honeydewsleep/wildchild/preview/matched_base_cut.png

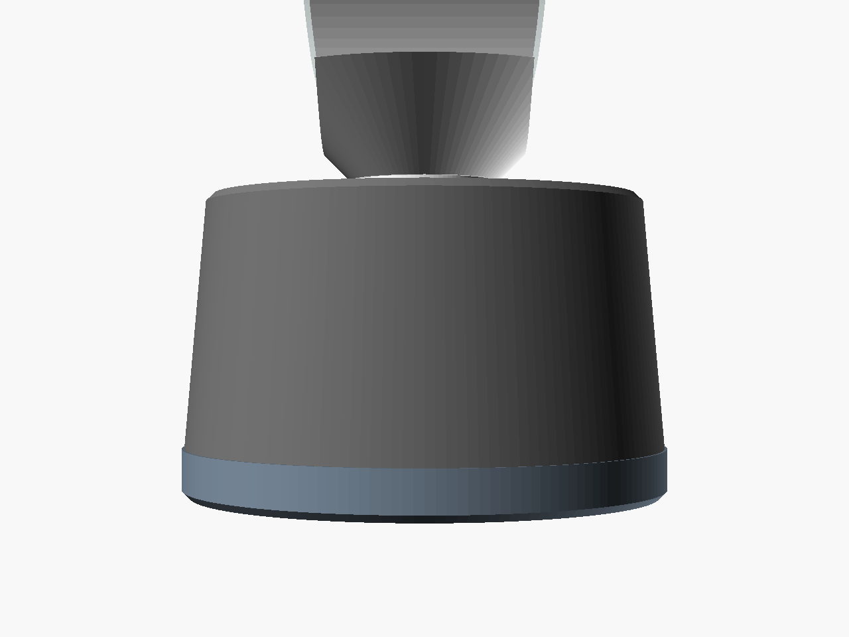
preview/matched_base_cut.png
