honeydewsleep/wildchild/preview/shape_options.png

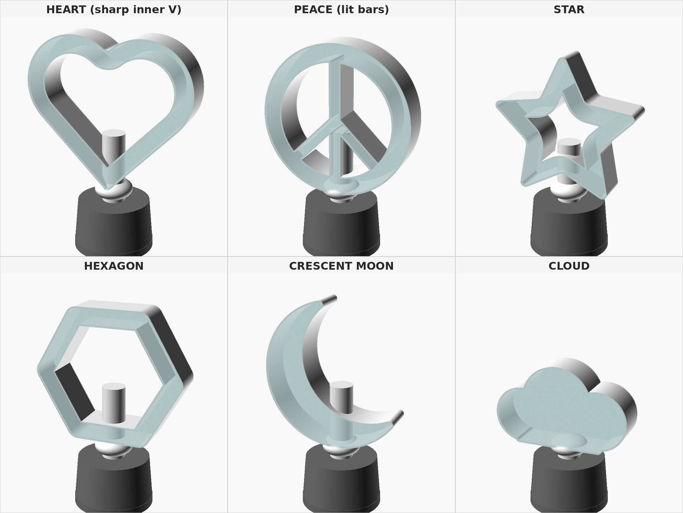
preview/shape_options.png
