honeydewsleep/wildchild/stl/capsule_funnel_00.stl

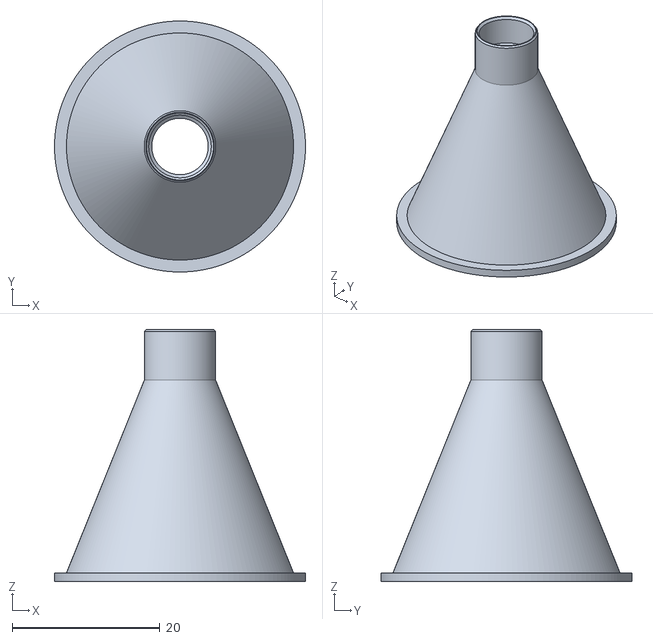
[picture p23: CAD file, 2026-10-06]
stl/capsule_funnel_00.stl
34.0 x 34.0 x 34.2
