honeydewsleep/wildchild/stl/shell_free_port_button.stl

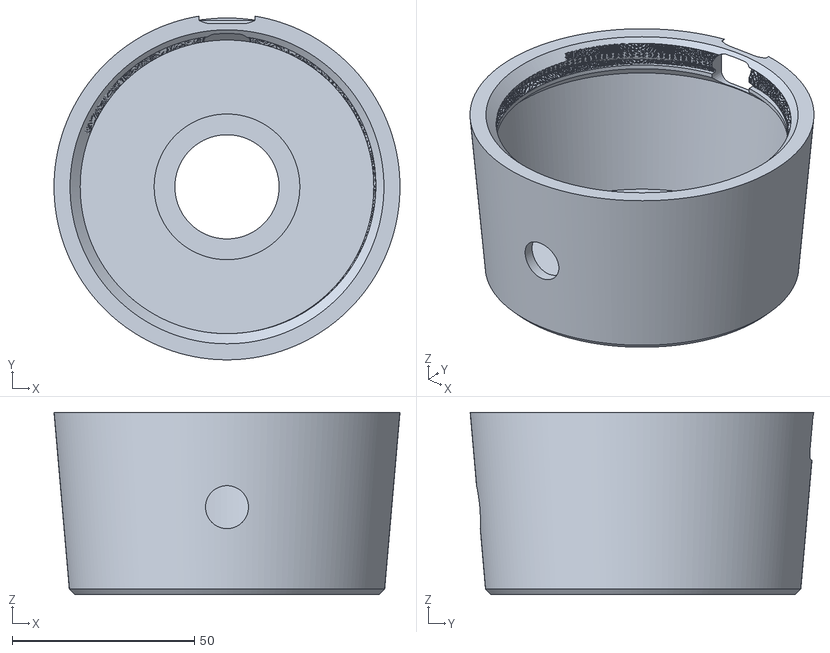
[picture p24: CAD file, 2026-08-14]
stl/shell_free_port_button.stl
95.0 x 94.4 x 50.0
