honeydewsleep/wildchild/stl/chassis_jack.stl

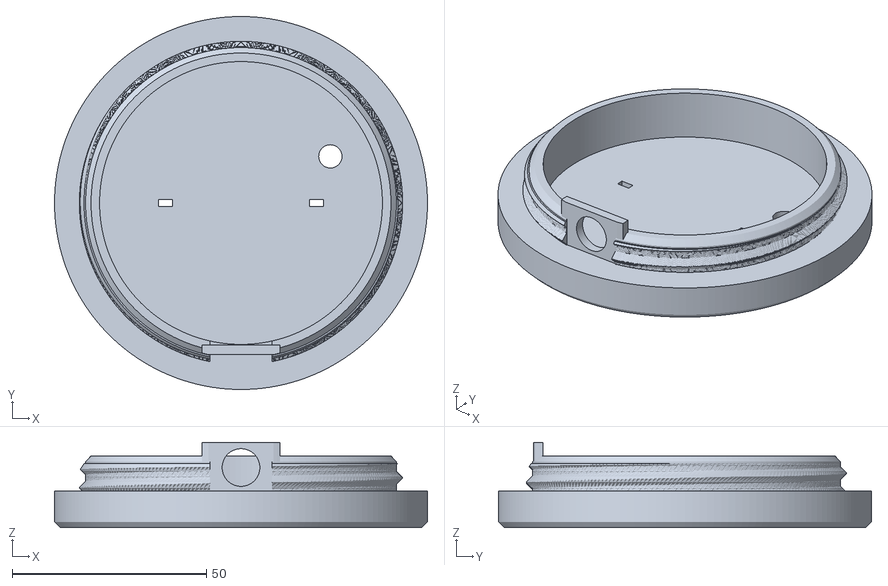
[picture p25: CAD file, 2026-08-14]
stl/chassis_jack.stl
96.0 x 96.0 x 22.0
