honeydewsleep/wildchild/stl/shell_free_jack_button.stl

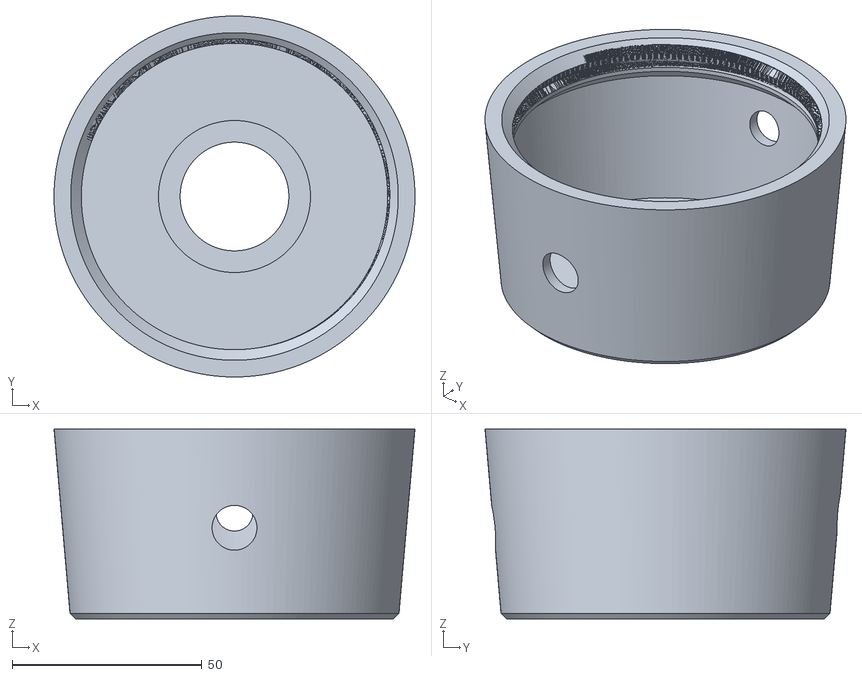
[picture p26: CAD file, 2026-08-13]
stl/shell_free_jack_button.stl
95.0 x 95.0 x 50.0
