honeydewsleep/wildchild/stl/shell_free_button7.stl

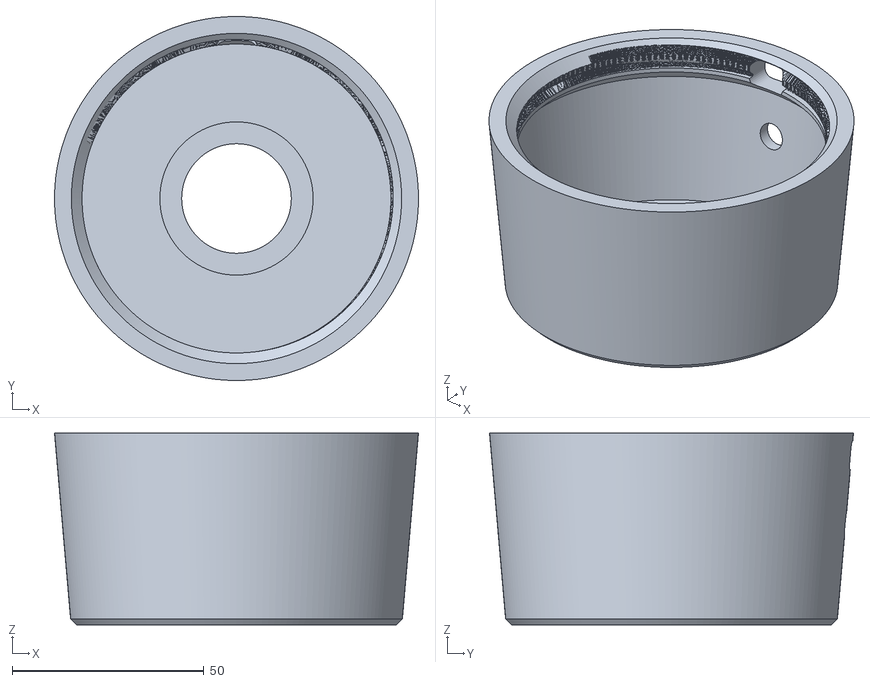
[picture p27: CAD file, 2026-08-11]
stl/shell_free_button7.stl
95.0 x 95.0 x 50.0
