honeydewsleep/wildchild/stl/ring_double_sided.stl

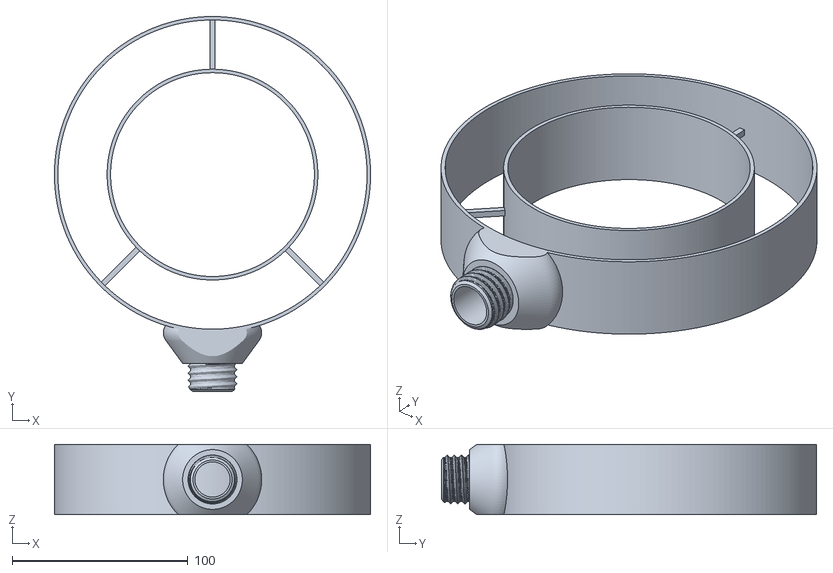
[picture p28: CAD file, 2026-07-26]
stl/ring_double_sided.stl
180.0 x 213.5 x 40.0
