honeydewsleep/wildchild/stl/ring_ds_diffuser.stl

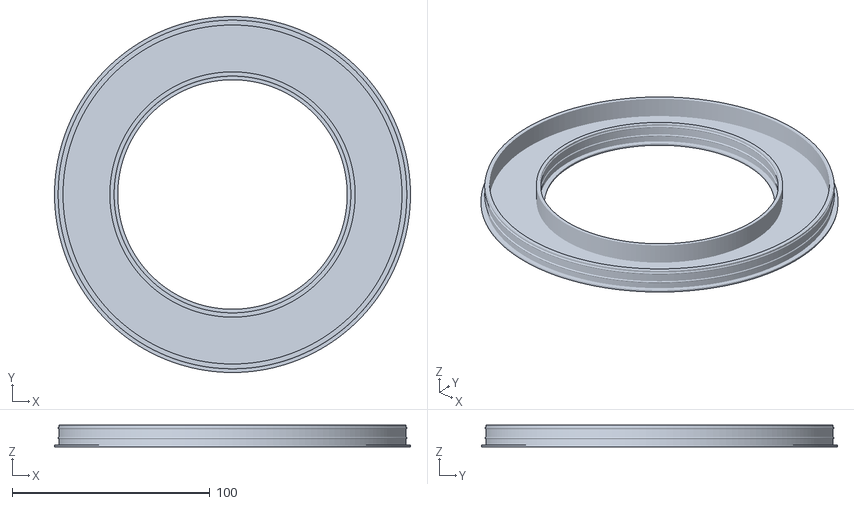
[picture p29: CAD file, 2026-07-26]
stl/ring_ds_diffuser.stl
180.0 x 180.0 x 11.0
