honeydewsleep/wildchild/stl/ring_diffuser.stl

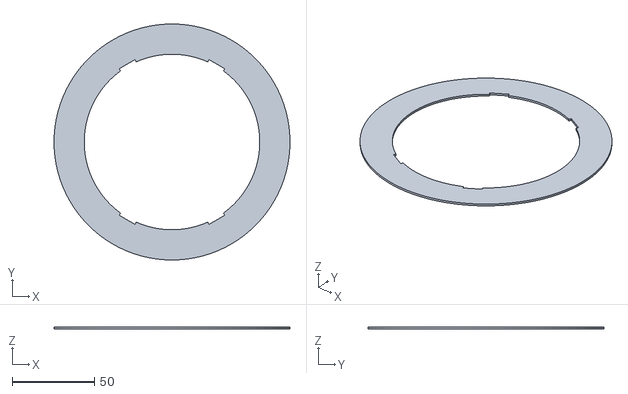
[picture p30: CAD file, 2026-07-26]
stl/ring_diffuser.stl
143.4 x 143.4 x 1.20
