honeydewsleep/wildchild/stl/stem_locknut.stl

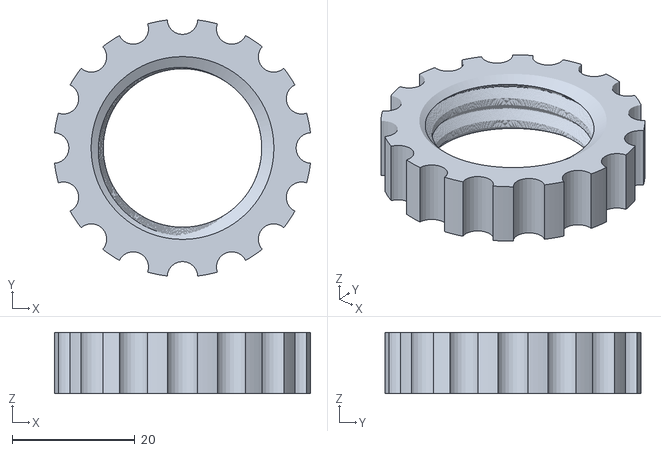
[picture p31: CAD file, 2026-07-26]
stl/stem_locknut.stl
41.7 x 41.7 x 10.0
