honeydewsleep/wildchild/stl/shell_threaded.stl

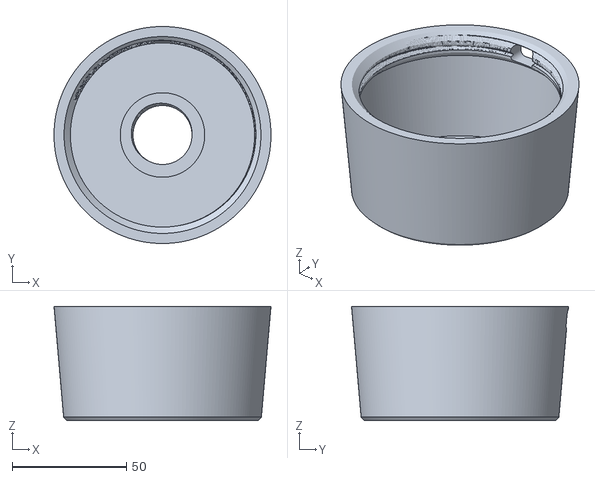
[picture p32: CAD file, 2026-07-26]
stl/shell_threaded.stl
95.0 x 95.0 x 50.0
