honeydewsleep/wildchild/stl/chassis_bat_flat8.stl

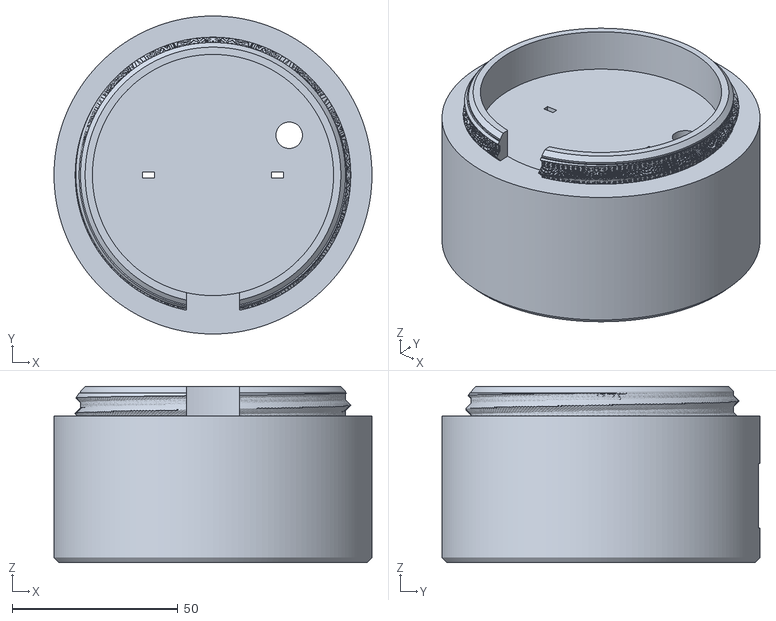
[picture p33: CAD file, 2026-07-25]
stl/chassis_bat_flat8.stl
96.0 x 96.0 x 53.2
