honeydewsleep/wildchild/stl/chassis_bat_flat4.stl

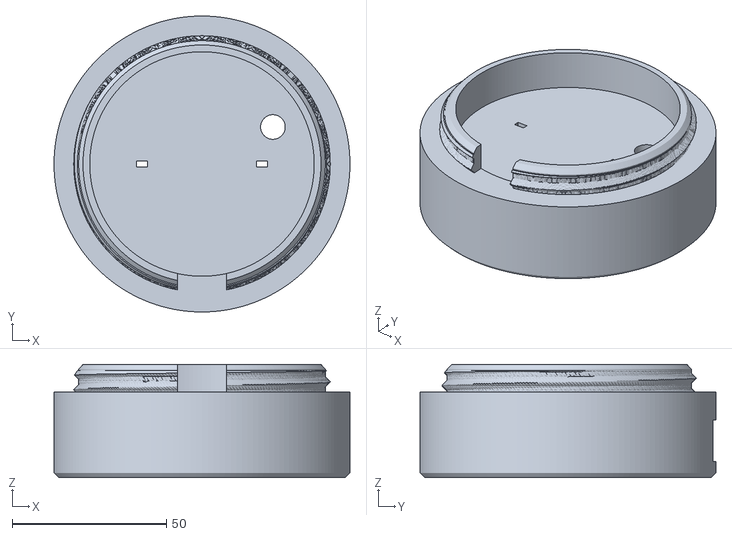
[picture p34: CAD file, 2026-07-25]
stl/chassis_bat_flat4.stl
96.0 x 96.0 x 36.7
