honeydewsleep/wildchild/stl/chassis.stl

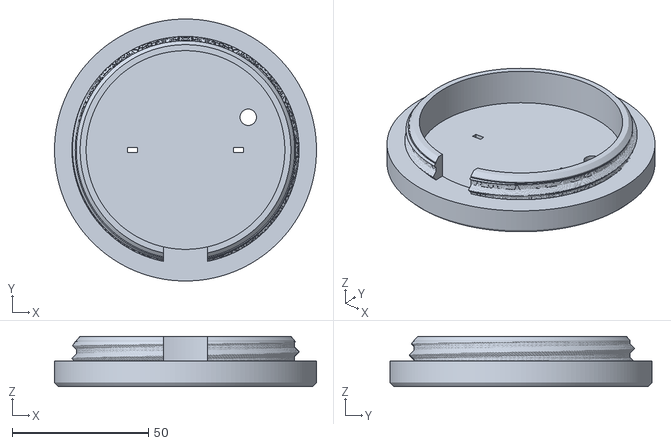
[picture p35: CAD file, 2026-07-25]
stl/chassis.stl
96.0 x 96.0 x 18.5
