honeydewsleep/wildchild/stl/chassis_bat_cube.stl

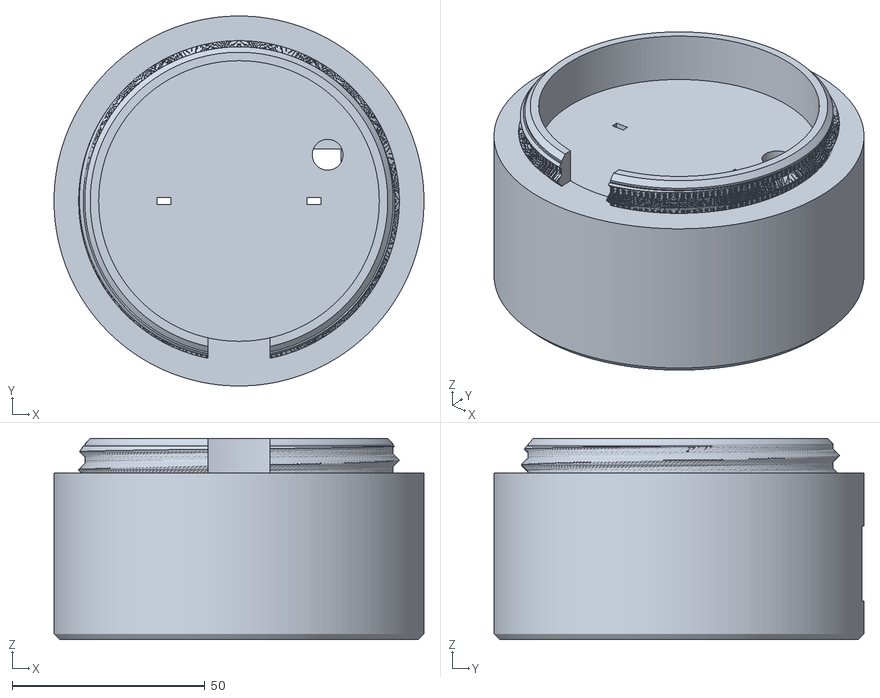
[picture p36: CAD file, 2026-07-25]
stl/chassis_bat_cube.stl
96.0 x 96.0 x 52.2
