honeydewsleep/wildchild/stl/battery_tub_4aa_cube.stl

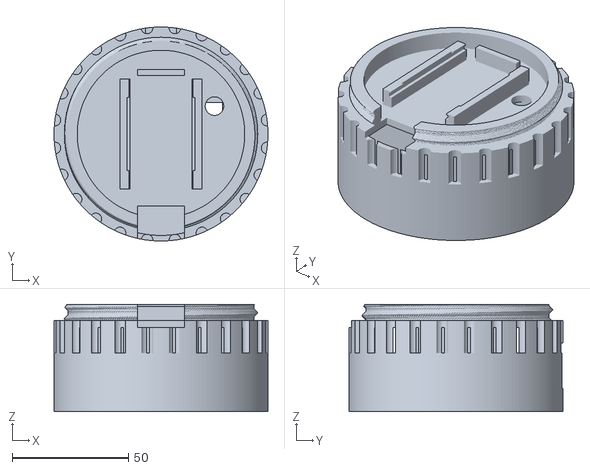
[picture p37: CAD file, 2026-07-25]
stl/battery_tub_4aa_cube.stl
92.0 x 92.0 x 46.2
