honeydewsleep/wildchild/stl/thread_test_collar.stl

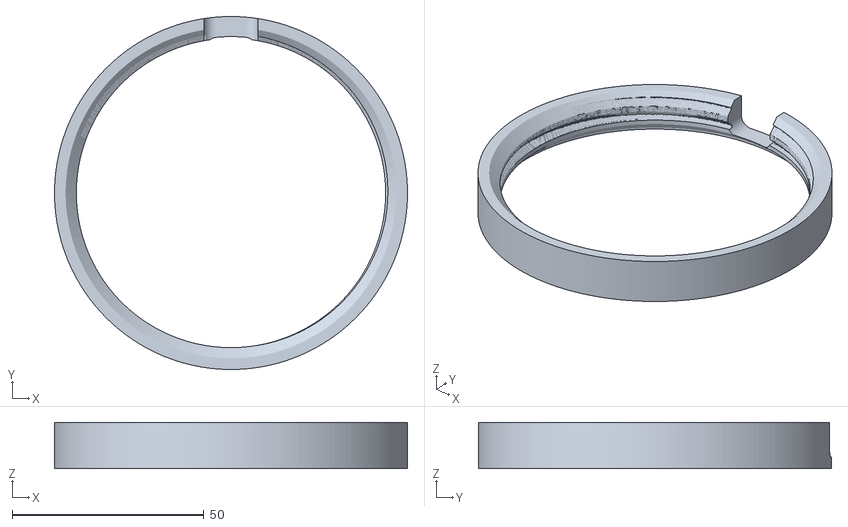
[picture p38: CAD file, 2026-07-25]
stl/thread_test_collar.stl
92.0 x 92.0 x 12.0
