honeydewsleep/wildchild/stl/battery_tub_4aa_flat.stl

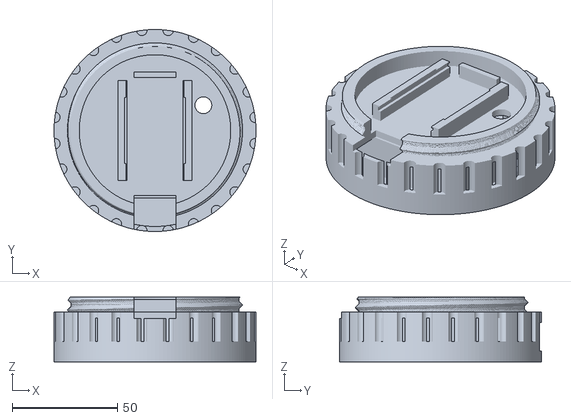
[picture p39: CAD file, 2026-07-25]
stl/battery_tub_4aa_flat.stl
96.0 x 96.0 x 30.7
