honeydewsleep/wildchild/stl/battery_door_flat.stl

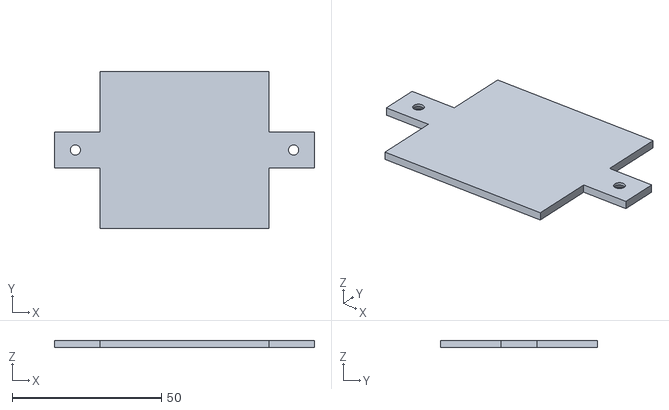
[picture p40: CAD file, 2026-07-25]
stl/battery_door_flat.stl
87.0 x 52.4 x 2.40
