honeydewsleep/wildchild/stl/bottom_plate.stl

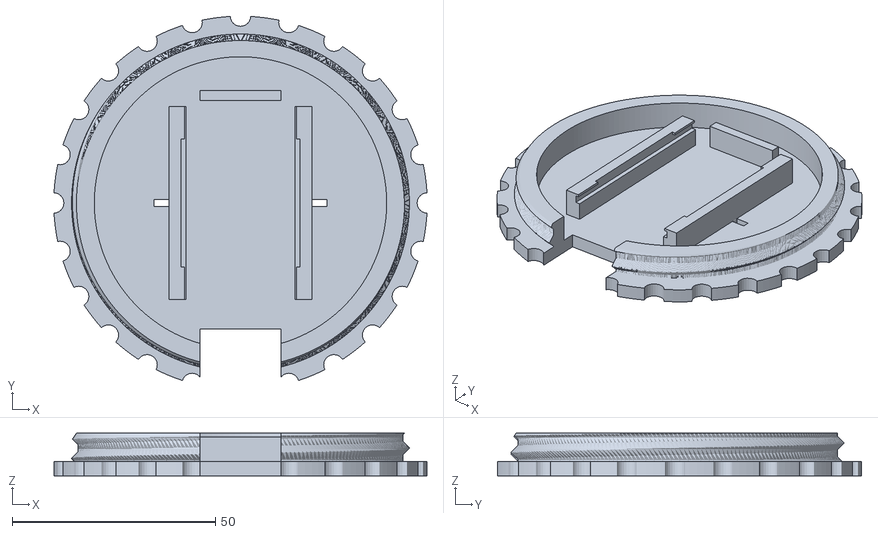
[picture p41: CAD file, 2026-07-25]
stl/bottom_plate.stl
91.8 x 89.6 x 10.5
