honeydewsleep/wildchild/stl/bottom_plate_plain.stl

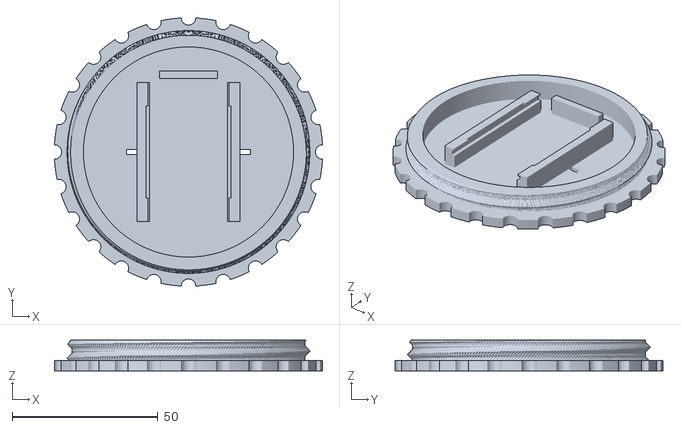
[picture p42: CAD file, 2026-07-25]
stl/bottom_plate_plain.stl
91.8 x 91.8 x 10.5
