honeydewsleep/wildchild/stl/battery_door_cube.stl

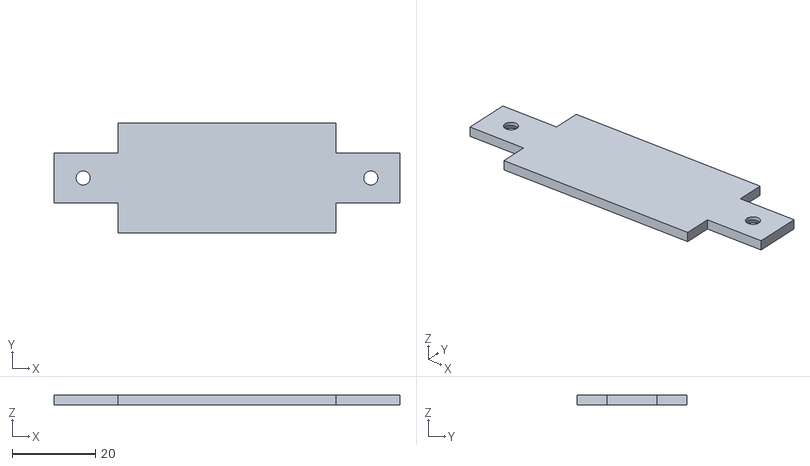
[picture p43: CAD file, 2026-07-25]
stl/battery_door_cube.stl
83.0 x 26.4 x 2.40
