honeydewsleep/wildchild/stl/base_wallhole.stl

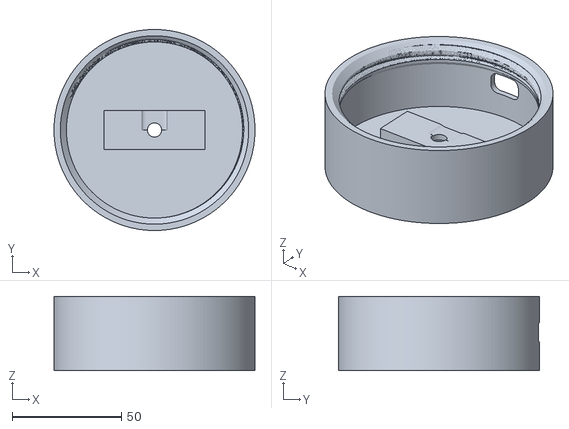
[picture p44: CAD file, 2026-07-25]
stl/base_wallhole.stl
92.0 x 92.0 x 34.0
