honeydewsleep/wildchild/stl/ring_half.stl

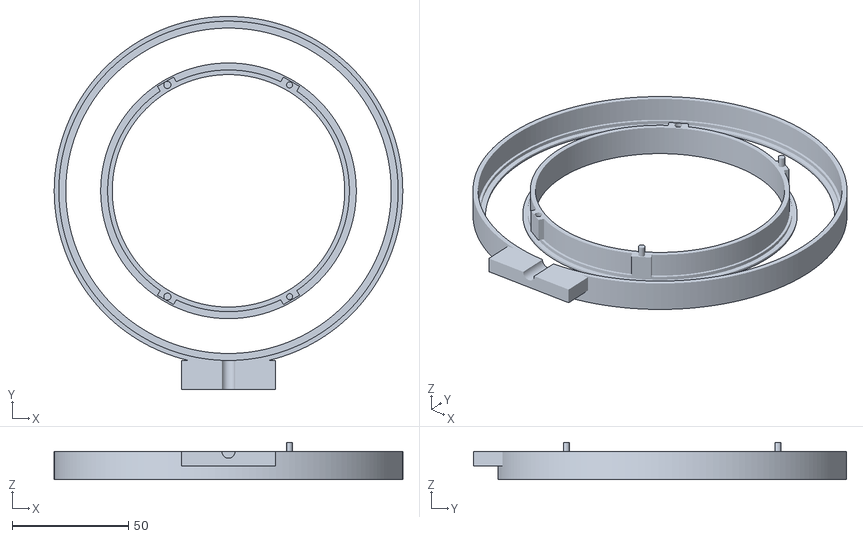
[picture p45: CAD file, 2026-07-25]
stl/ring_half.stl
150.0 x 160.5 x 16.0
