honeydewsleep/wildchild/stl/battery_tub_8aa_flat.stl

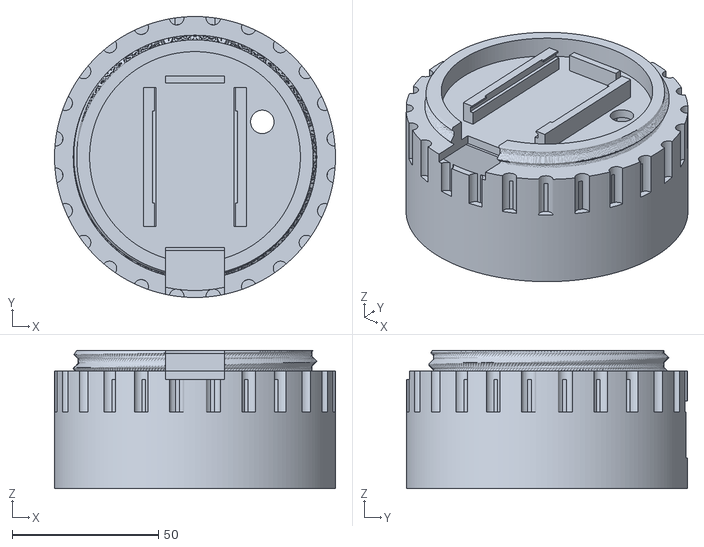
[picture p46: CAD file, 2026-07-25]
stl/battery_tub_8aa_flat.stl
96.0 x 96.0 x 47.2
