honeydewsleep/wildchild/preview/assembly_battery.png

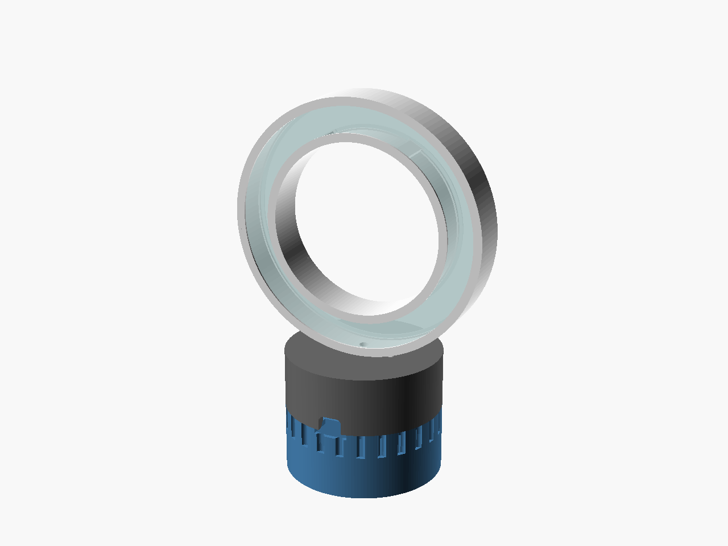
preview/assembly_battery.png
