honeydewsleep/wildchild/preview/assembly_matched.png

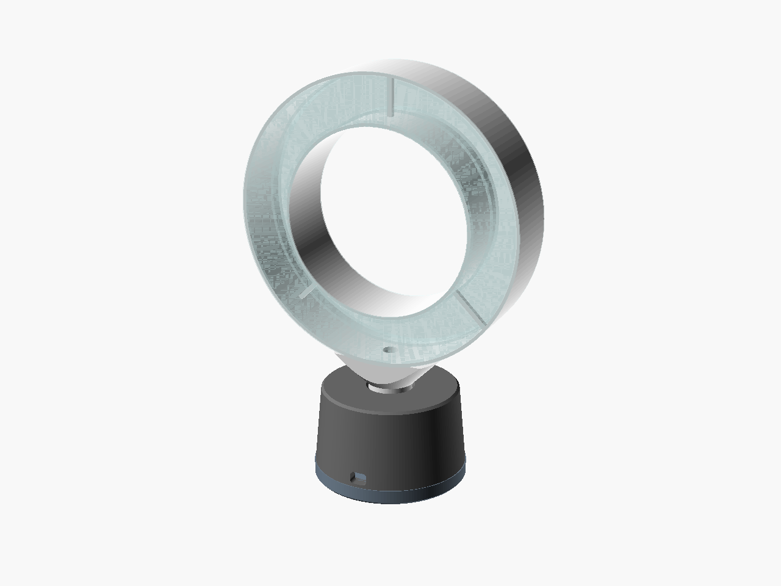
preview/assembly_matched.png
